robinhedwards/UnoCart-2600/source/STM32firmware/Atari2600Cart/src/firmware_ntsc_rom.h

unsigned const char firmware_ntsc_rom[] = {
  0xd8, 0xa9, 0x00, 0xaa, 0x95, 0x00, 0xe8, 0xd0, 0xfb, 0xca, 0x9a, 0xad,
  0xf4, 0x1f, 0x20, 0x49, 0xf2, 0xa2, 0xf0, 0x20, 0x84, 0x00, 0x20, 0x27,
  0xf0, 0x20, 0xb9, 0xf0, 0x20, 0x49, 0xf2, 0xa6, 0x80, 0x20, 0x84, 0x00,
  0x4c, 0x16, 0xf0, 0xa9, 0x00, 0x85, 0xac, 0x85, 0x80, 0x85, 0xa9, 0x85,
  0xa8, 0xa9, 0x00, 0x85, 0xa6, 0xa9, 0xf8, 0x85, 0xa7, 0xa0, 0x00, 0xb1,
  0xa6, 0xf0, 0x12, 0x18, 0x18, 0xa5, 0xa6, 0x69, 0x0c, 0x85, 0xa6, 0x90,
  0x02, 0xe6, 0xa7, 0xe6, 0xa8, 0xa5, 0xa8, 0xd0, 0xea, 0x60, 0xa5, 0xac,
  0xf0, 0x03, 0xc6, 0xac, 0x60, 0xa9, 0x20, 0x2d, 0x80, 0x02, 0xf0, 0x0a,
  0xa9, 0x02, 0x2d, 0x82, 0x02, 0xf0, 0x03, 0x4c, 0x77, 0xf0, 0xa6, 0x80,
  0xe8, 0xe4, 0xa8, 0xf0, 0x06, 0xe6, 0x80, 0xa9, 0x0a, 0x85, 0xac, 0xa9,
  0x10, 0x2d, 0x80, 0x02, 0xd0, 0x0a, 0xa6, 0x80, 0xf0, 0x06, 0xc6, 0x80,
  0xa9, 0x0a, 0x85, 0xac, 0xa9, 0x40, 0x2d, 0x80, 0x02, 0xd0, 0x0f, 0xa5,
  0x80, 0xc9, 0x07, 0x90, 0x09, 0x38, 0xe9, 0x07, 0x85, 0x80, 0xa9, 0x0a,
  0x85, 0xac, 0xa9, 0x80, 0x2d, 0x80, 0x02, 0xd0, 0x13, 0xa5, 0x80, 0x18,
  0x69, 0x07, 0xc5, 0xa8, 0x90, 0x04, 0xa4, 0xa8, 0x88, 0x98, 0x85, 0x80,
  0xa9, 0x0a, 0x85, 0xac, 0x60, 0xa9, 0x00, 0x85, 0x08, 0xa9, 0x70, 0x85,
  0x0d, 0xa9, 0x00, 0x85, 0x0e, 0xa9, 0x00, 0x85, 0x0f, 0xa9, 0x01, 0x85,
  0x0a, 0xa9, 0x02, 0x85, 0x01, 0x85, 0x00, 0x85, 0x02, 0x85, 0x02, 0x85,
  0x02, 0xa9, 0x00, 0x85, 0x00, 0xa9, 0x2a, 0x85, 0x02, 0x8d, 0x96, 0x02,
  0x20, 0x52, 0xf0, 0xc6, 0x88, 0xa9, 0x01, 0x85, 0x25, 0x85, 0x26, 0xa9,
  0x06, 0x85, 0x04, 0x85, 0x05, 0xa9, 0x15, 0xa2, 0x00, 0x20, 0x00, 0xf3,
  0xa9, 0x25, 0xa2, 0x01, 0x20, 0x00, 0xf3, 0xa9, 0x00, 0x85, 0xa6, 0xa9,
  0xf8, 0x85, 0xa7, 0xa9, 0x00, 0x85, 0x8c, 0x85, 0xa9, 0xa5, 0x80, 0x85,
  0xa5, 0x38, 0xe9, 0x07, 0x30, 0x19, 0x85, 0xa5, 0xa5, 0xa9, 0x18, 0x69,
  0x07, 0x85, 0xa9, 0x18, 0xa5, 0xa6, 0x69, 0x54, 0x85, 0xa6, 0x90, 0x02,
  0xe6, 0xa7, 0xa5, 0xa5, 0x4c, 0x15, 0xf1, 0x85, 0x02, 0xad, 0x84, 0x02,
  0xd0, 0xfb, 0x85, 0x02, 0xa9, 0x00, 0x85, 0x02, 0x85, 0x01, 0x85, 0x02,
  0xa9, 0xe2, 0x85, 0x02, 0x8d, 0x96, 0x02, 0xa9, 0x00, 0x85, 0x8a, 0xa9,
  0xf7, 0x85, 0x8b, 0xa9, 0x00, 0x85, 0x8c, 0x20, 0x19, 0xf3, 0xa9, 0x9e,
  0x85, 0x06, 0x85, 0x07, 0xa9, 0x94, 0x85, 0x02, 0x85, 0x09, 0x20, 0x3f,
  0xf3, 0xa9, 0x00, 0x85, 0xab, 0x85, 0x8c, 0xa9, 0x00, 0x85, 0x02, 0x85,
  0x09, 0xa5, 0xa9, 0x18, 0x65, 0xab, 0x85, 0xaa, 0xc5, 0xa8, 0xb0, 0x44,
  0xa5, 0xa6, 0x85, 0x8a, 0xa5, 0xa7, 0x85, 0x8b, 0x20, 0x19, 0xf3, 0x85,
  0x02, 0xa5, 0xaa, 0xc5, 0x80, 0xd0, 0x09, 0xa2, 0xce, 0xa0, 0xc2, 0xa9,
  0xce, 0x4c, 0xaf, 0xf1, 0xa4, 0x8c, 0xb1, 0x8a, 0x29, 0x80, 0xf0, 0x07,
  0xa2, 0x9a, 0xa0, 0x80, 0x4c, 0xaf, 0xf1, 0xa2, 0x0e, 0xa0, 0x80, 0x86,
  0x06, 0x86, 0x07, 0x85, 0x02, 0x84, 0x09, 0x20, 0x3f, 0xf3, 0xa5, 0x8c,
  0x18, 0x69, 0x0c, 0x85, 0x8c, 0x4c, 0xde, 0xf1, 0xa9, 0x0c, 0x85, 0x8a,
  0xa9, 0xf7, 0x85, 0x8b, 0xa9, 0x00, 0x85, 0x8c, 0x20, 0x19, 0xf3, 0xa9,
  0x80, 0x85, 0x02, 0x85, 0x09, 0x20, 0x3f, 0xf3, 0x85, 0x02, 0xe6, 0xab,
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
};
unsigned int firmware_ntsc_rom_len = 4096;
