robinhedwards/UnoCart-2600/source/STM32firmware/Atari2600Cart/src/cartridge_supercharger.h

#ifndef CARTRIDGE_SUPERCHARGER_H
#define CARTRIDGE_SUPERCHARGER_H

void emulate_supercharger_cartridge(const char* filename, unsigned int image_size, uint8_t *buffer, int tv_mode);

#endif // CARTRIDGE_SUPERCHARGER_H
